MonkeyCodeMen/ULC-Pico-C-Code/include/MainConfig.h

#pragma once
#include <Arduino.h>


/*****************************************************************
 * 
 *   main project configuration 
 *  
 *****************************************************************/
///////////////////////////////////////////
// Application configs   

// my VS-Code terminal needs some time after download to open
// so the setup will wait for this time before executing setup, so that all 
// debug logs are visibile in the terminal
#define WAIT_FOR_TERMINAL           4000  //[ms]    

#define BLINK_SEQ_MAIN              {250, 500, 250, 500, 500, 1000}

#define WITH_DSIPLAY_STARTUP_TEST
//#define PRINT_LOOP_STATS    10000




///////////////////////////////////////////
// uinty test configs   
#define WAIT_FOR_UINTY_FRAMEWORK    2000  // [ms]
#define BLINK_SEQ_TEST              {500, 1000, 50, 500, 50, 250, 50, 125}


///////////////////////////////////////////
// common configs   

#define I2C_100KHZ  100*1000
#define I2C_400KHZ  400*1000
#define I2C_DEFAULT_SPEED   I2C_400KHZ
